LCobeaga/Auto_Rifles/parts/cages and wheels/flywheel smooth 1806.stl

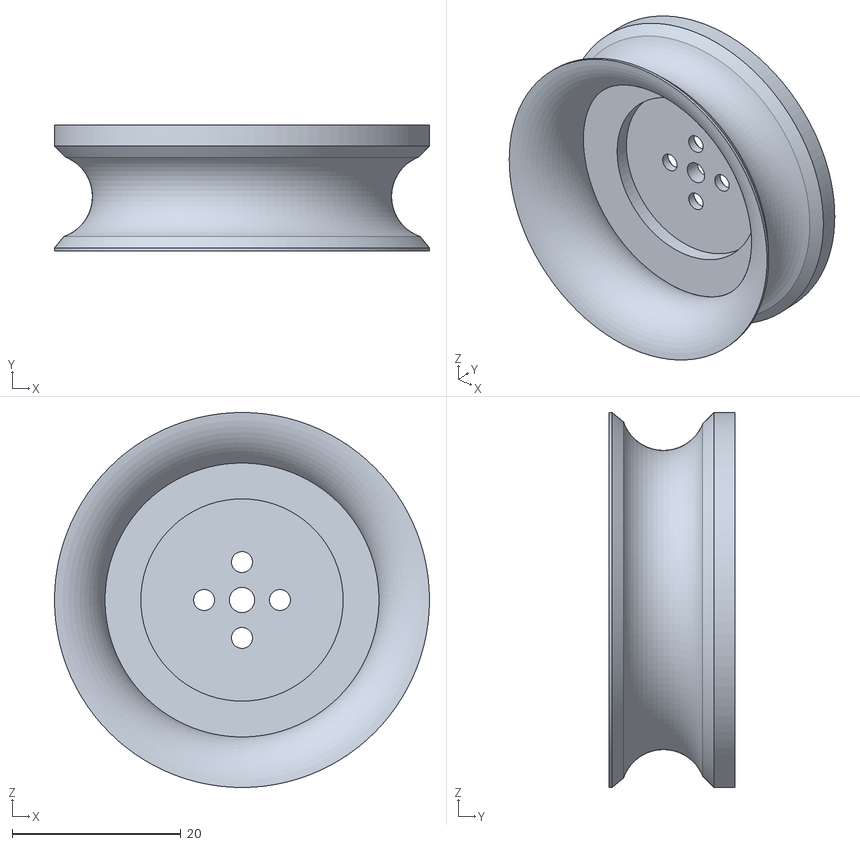
[picture p15: CAD file, 2020-12-02]
parts/cages and wheels/flywheel smooth 1806.stl
44.5 x 15.0 x 44.5
