LCobeaga/Auto_Rifles/parts/front barrel support.stl

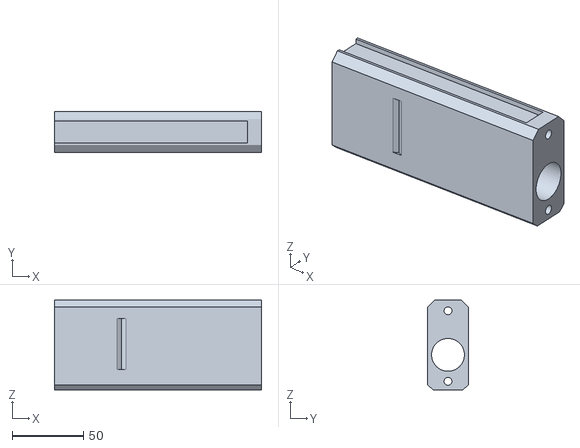
[picture p16: CAD file, 2021-01-24]
parts/front barrel support.stl
145.0 x 28.6 x 63.0
