LCobeaga/Auto_Rifles/parts/Shadow_Price_panels/Stripe right.stl

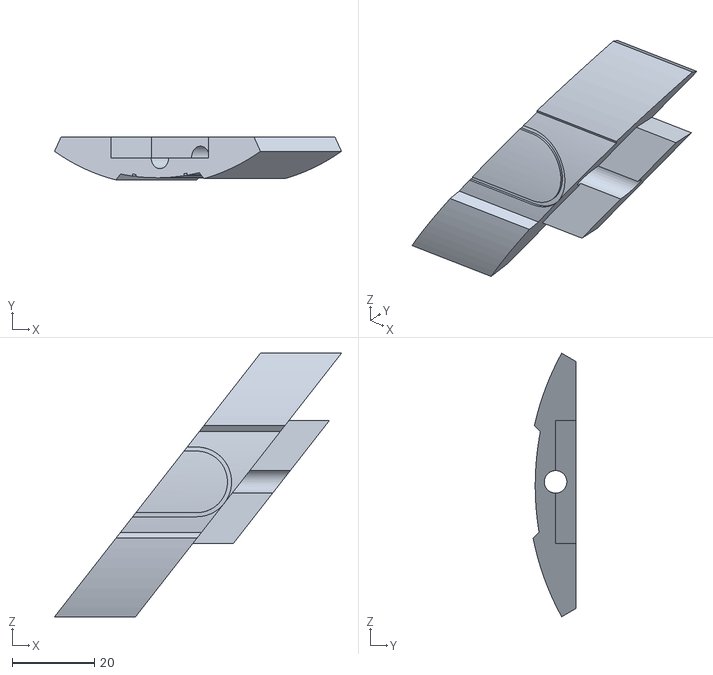
[picture p17: CAD file, 2021-04-09]
parts/Shadow_Price_panels/Stripe right.stl
69.9 x 10.4 x 64.2
