LCobeaga/Auto_Rifles/parts/battery tray.stl

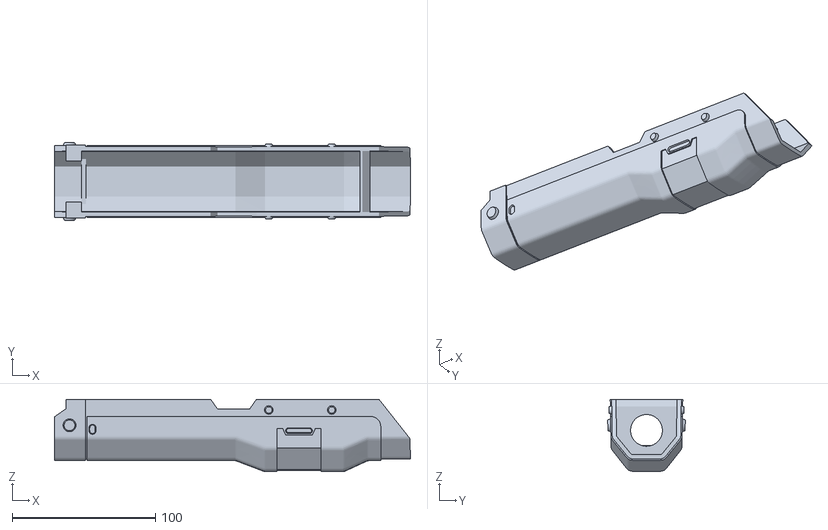
[picture p18: CAD file, 2021-01-12]
parts/battery tray.stl
248.8 x 54.3 x 50.7
