LCobeaga/Auto_Rifles/parts/custom panels/left panel basic.step

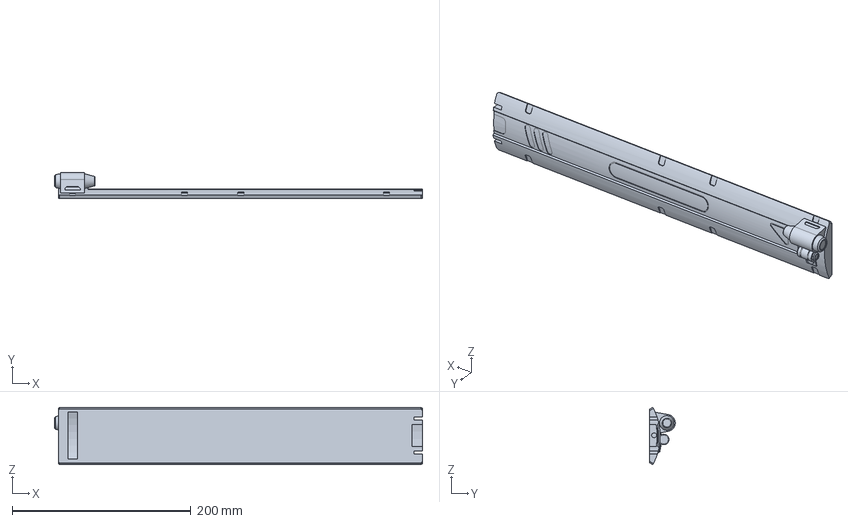
[picture p19: CAD file, 2020-12-09]
parts/custom panels/left panel basic.step
411.5 x 28.7 x 64.2 mm
