LCobeaga/Auto_Rifles/parts/Shadow_Price_panels/Triangle right.stl

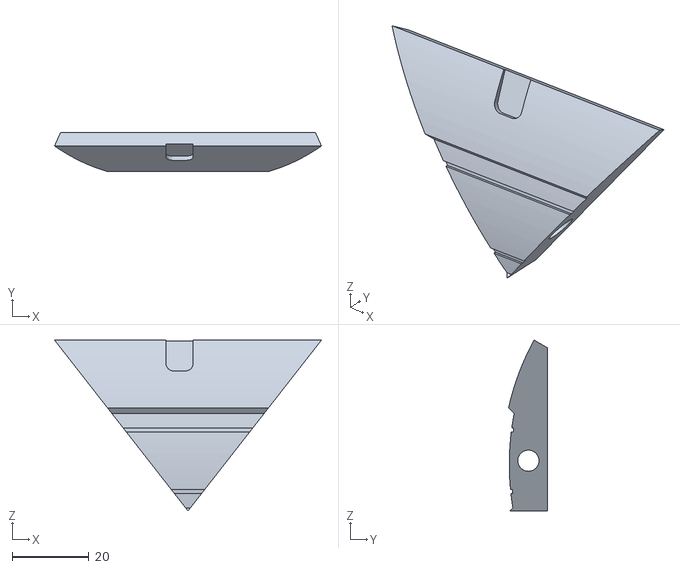
[picture p20: CAD file, 2021-04-09]
parts/Shadow_Price_panels/Triangle right.stl
69.4 x 10.1 x 44.4
