LCobeaga/Auto_Rifles/parts/custom panels/barrel clip modified.step

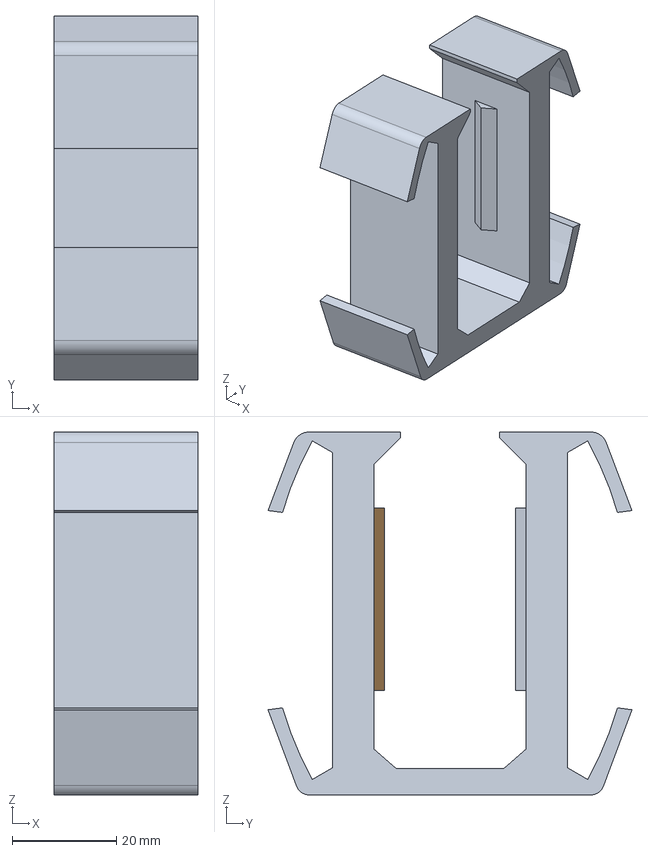
[picture p21: CAD file, 2020-12-09]
parts/custom panels/barrel clip modified.step
27.6 x 69.8 x 69.6 mm
