LCobeaga/Auto_Rifles/parts/lower.stl

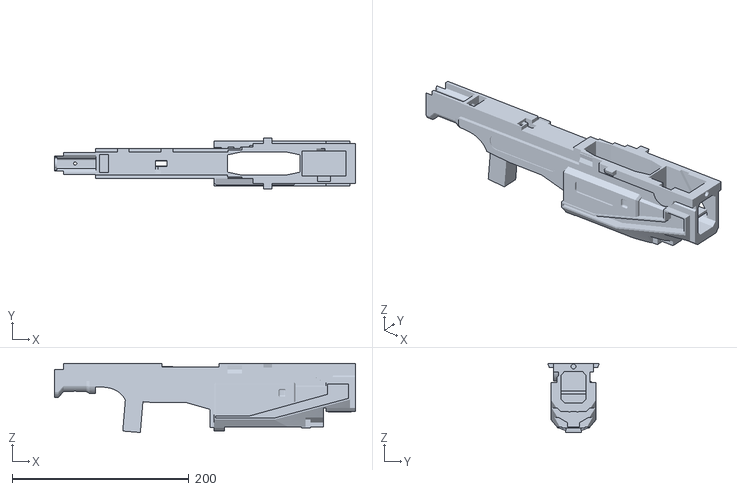
[picture p22: CAD file, 2020-12-02]
parts/lower.stl
340.8 x 58.3 x 78.2
