LCobeaga/Auto_Rifles/parts/Shadow_Price_panels/V left.stl

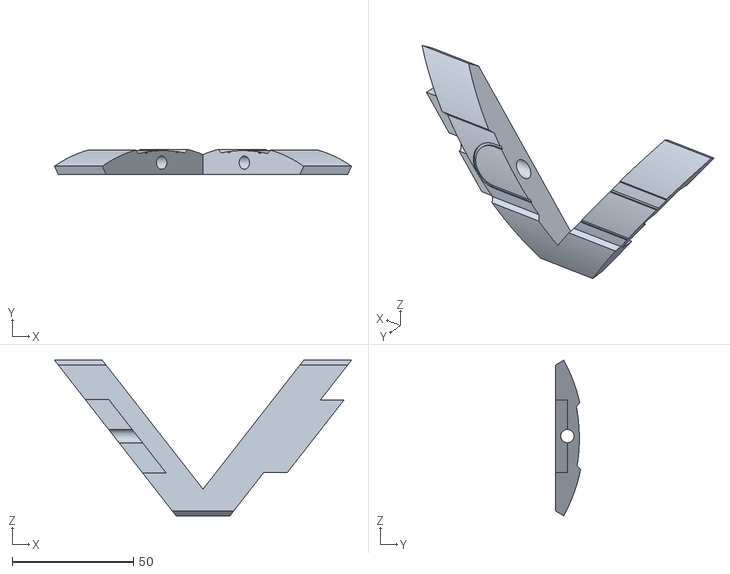
[picture p23: CAD file, 2021-04-09]
parts/Shadow_Price_panels/V left.stl
122.7 x 10.4 x 64.2
