LCobeaga/Auto_Rifles/parts/top cowl.stl

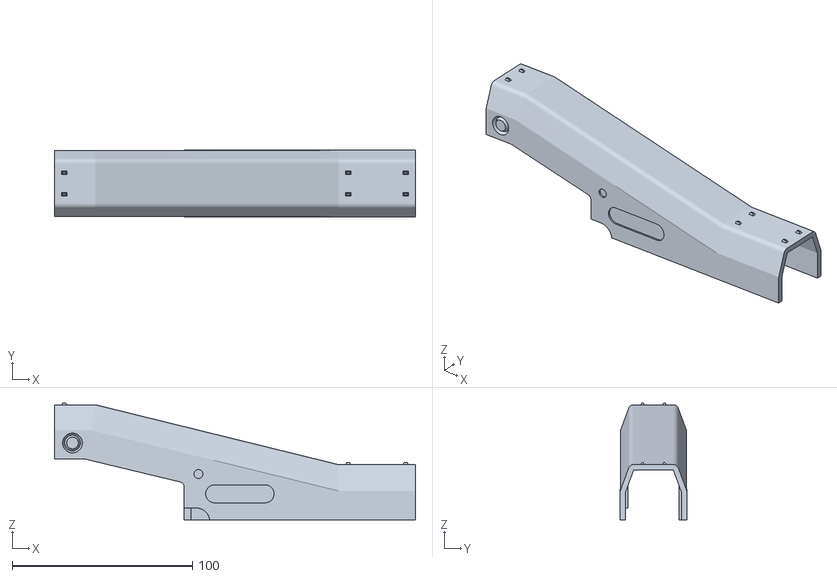
[picture p24: CAD file, 2020-12-02]
parts/top cowl.stl
200.4 x 37.1 x 64.9
