LCobeaga/Auto_Rifles/parts/Shadow_Price_panels/V right.stl

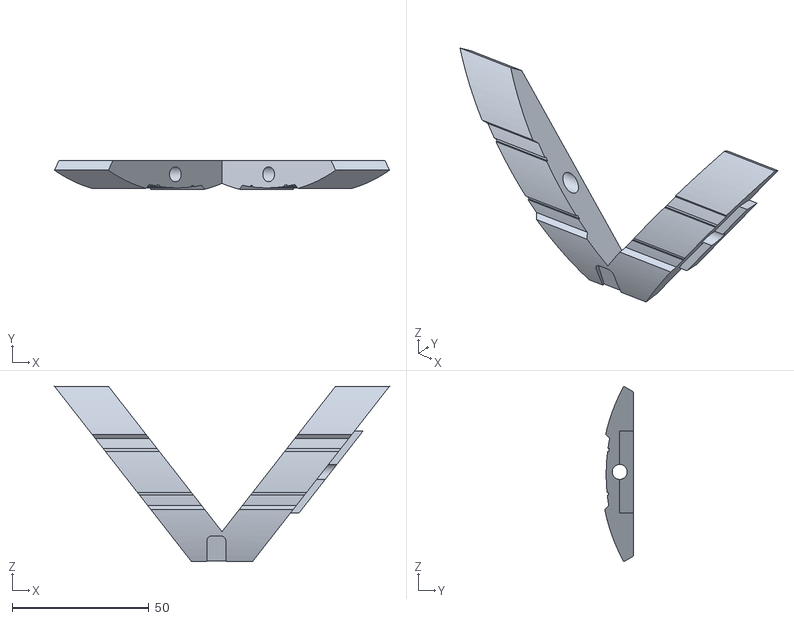
[picture p25: CAD file, 2021-04-09]
parts/Shadow_Price_panels/V right.stl
122.7 x 10.4 x 64.2
