LCobeaga/Auto_Rifles/parts/upper.stl

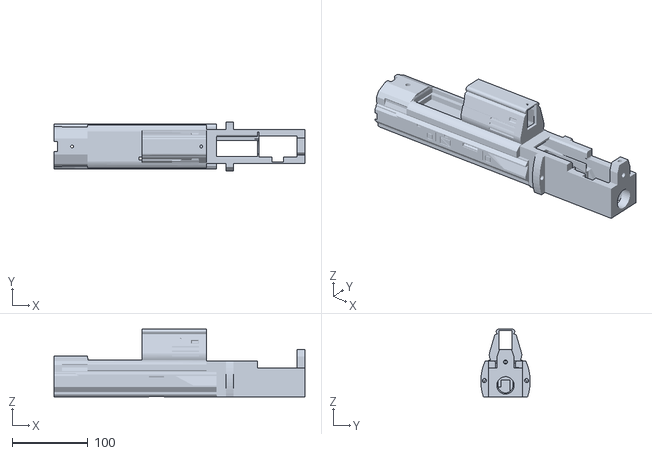
[picture p26: CAD file, 2020-12-02]
parts/upper.stl
331.1 x 65.0 x 89.4
