LCobeaga/Auto_Rifles/parts/archway.stl

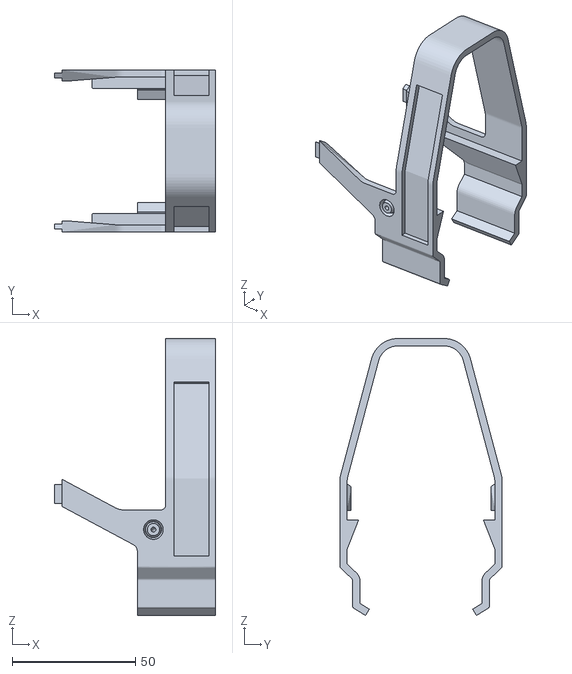
[picture p27: CAD file, 2020-12-02]
parts/archway.stl
65.5 x 66.0 x 112.6
