LCobeaga/Auto_Rifles/parts/Shadow_Price_panels/Back right.stl

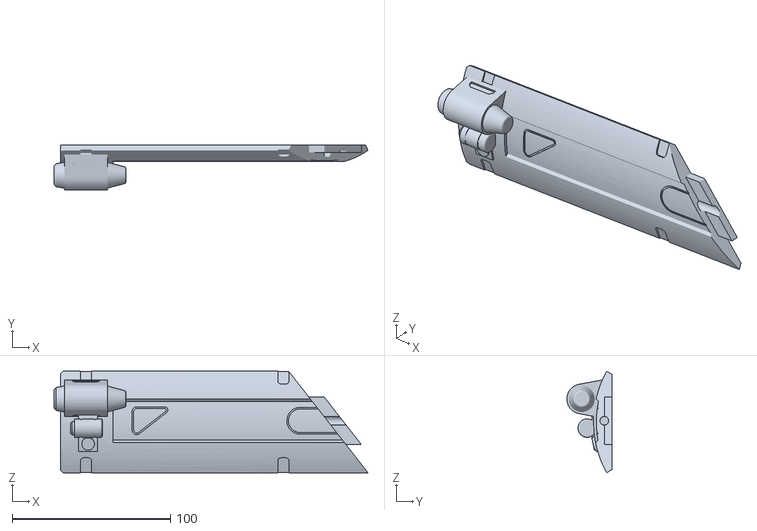
[picture p28: CAD file, 2021-04-09]
parts/Shadow_Price_panels/Back right.stl
198.7 x 28.6 x 64.2
