LCobeaga/Auto_Rifles/parts/Shadow_Price_panels/Stripe Gap right.stl

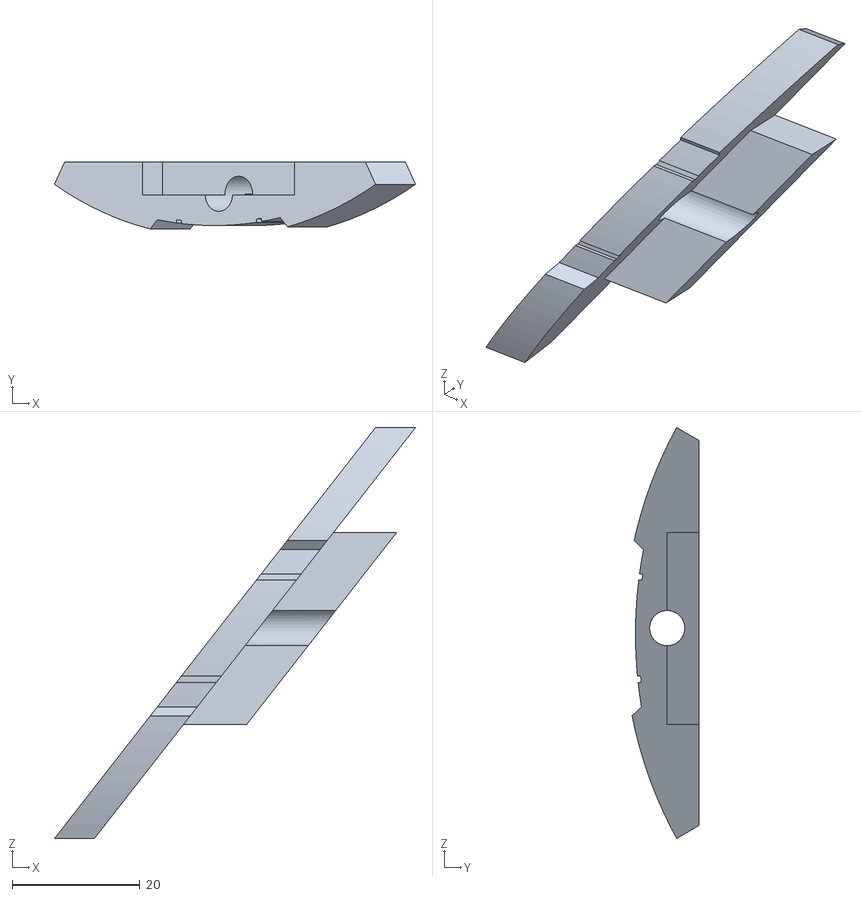
[picture p29: CAD file, 2021-04-09]
parts/Shadow_Price_panels/Stripe Gap right.stl
56.4 x 10.4 x 64.2
