LCobeaga/Auto_Rifles/parts/tail.stl

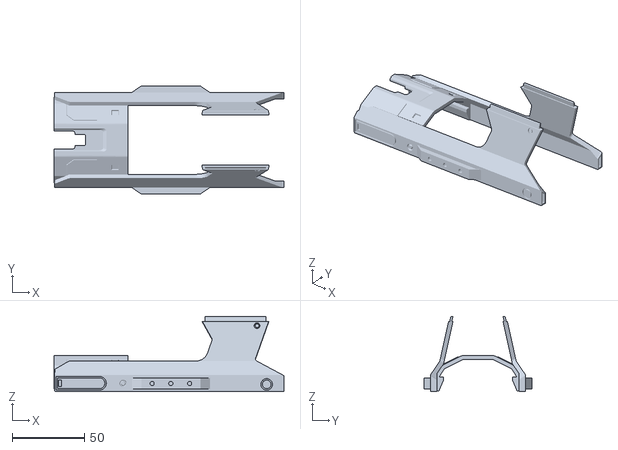
[picture p30: CAD file, 2020-12-02]
parts/tail.stl
159.4 x 75.0 x 52.1
