LCobeaga/Auto_Rifles/parts/2x upper detail.stl

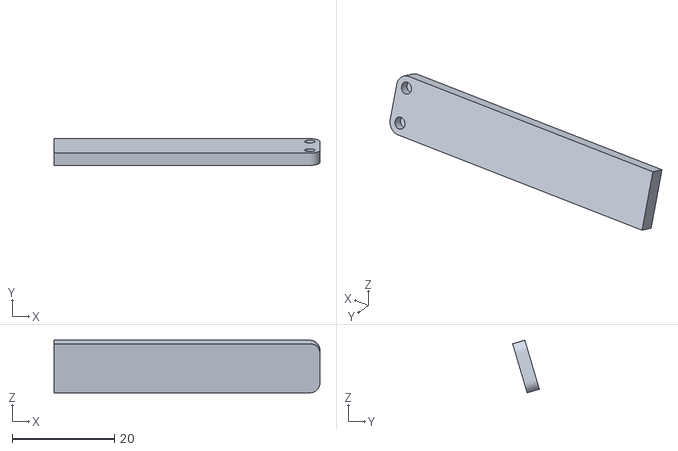
[picture p31: CAD file, 2020-12-02]
parts/2x upper detail.stl
52.0 x 5.24 x 10.3
