LCobeaga/Auto_Rifles/parts/Shadow_Price_panels/Stripe Gap left.stl

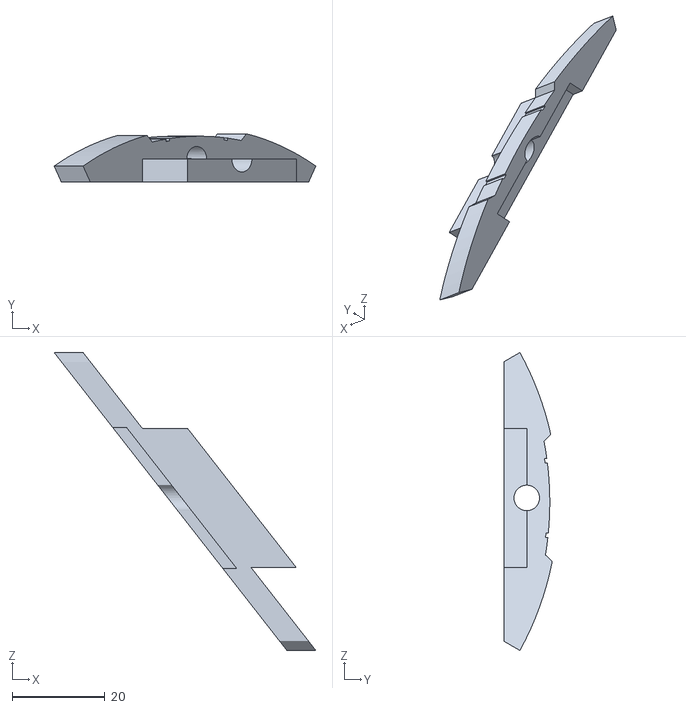
[picture p32: CAD file, 2021-04-09]
parts/Shadow_Price_panels/Stripe Gap left.stl
56.4 x 10.4 x 64.2
