LCobeaga/Auto_Rifles/parts/trigger.stl

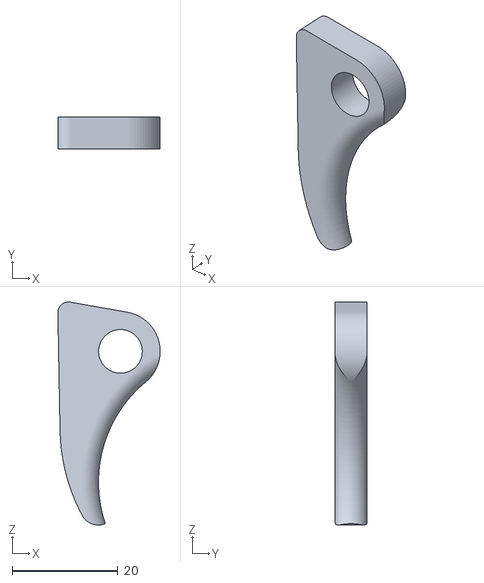
[picture p33: CAD file, 2020-12-02]
parts/trigger.stl
19.3 x 6.00 x 42.1
