LCobeaga/Auto_Rifles/parts/left stock plate.stl

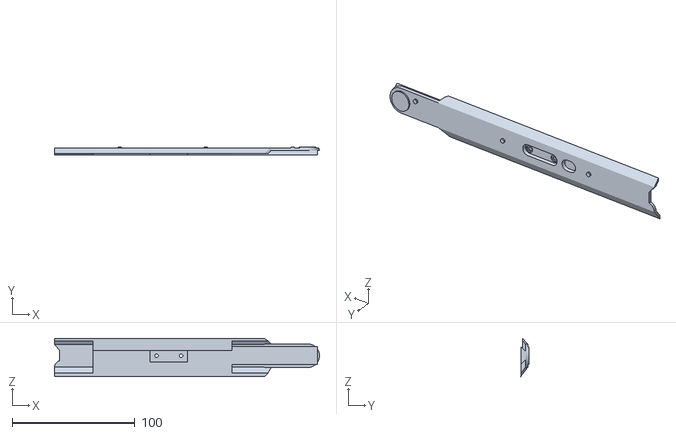
[picture p34: CAD file, 2020-12-02]
parts/left stock plate.stl
216.0 x 6.89 x 31.0
