LCobeaga/Auto_Rifles/parts/mag tooth.stl

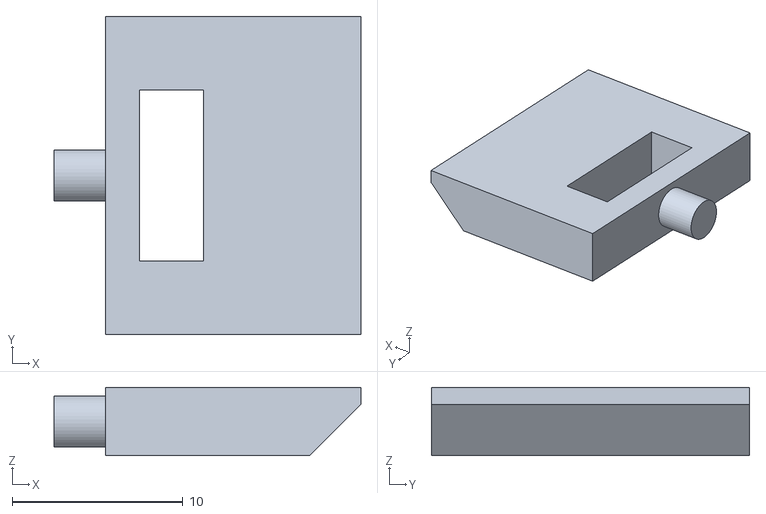
[picture p35: CAD file, 2020-12-02]
parts/mag tooth.stl
17.9 x 18.6 x 4.00
