LCobeaga/Auto_Rifles/parts/middle right loop.stl

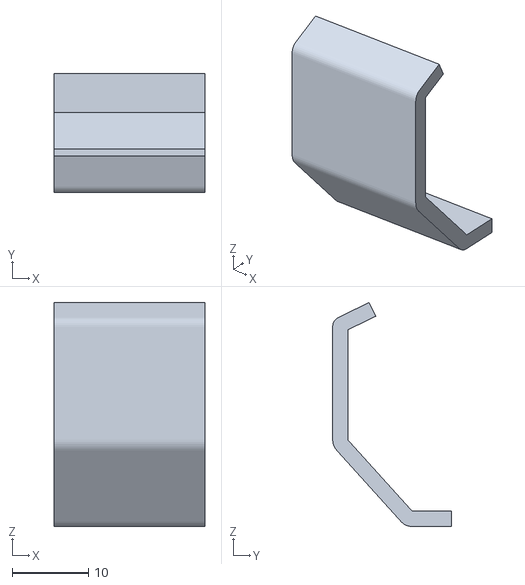
[picture p36: CAD file, 2020-12-02]
parts/middle right loop.stl
19.7 x 15.6 x 29.3
