LCobeaga/Auto_Rifles/parts/knuckle guard bottom.stl

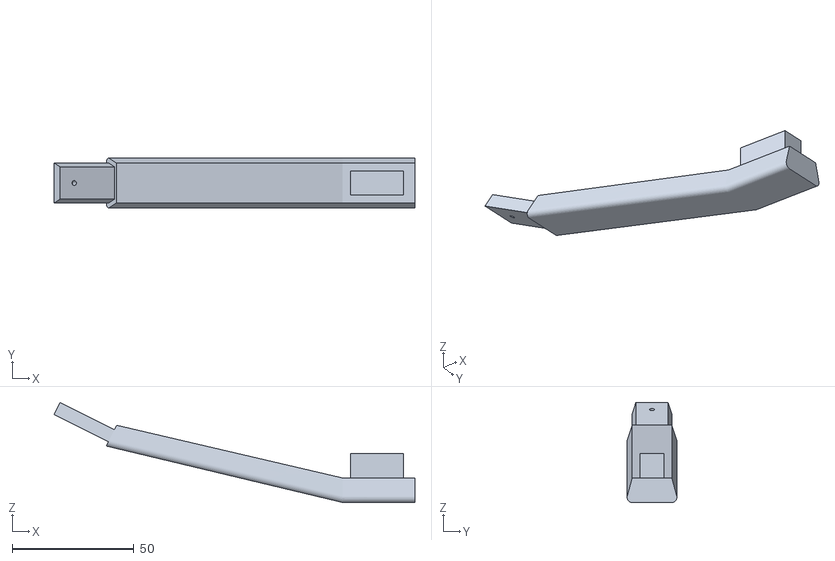
[picture p37: CAD file, 2020-12-02]
parts/knuckle guard bottom.stl
148.5 x 20.5 x 41.1
