LCobeaga/Auto_Rifles/parts/lower filler.stl

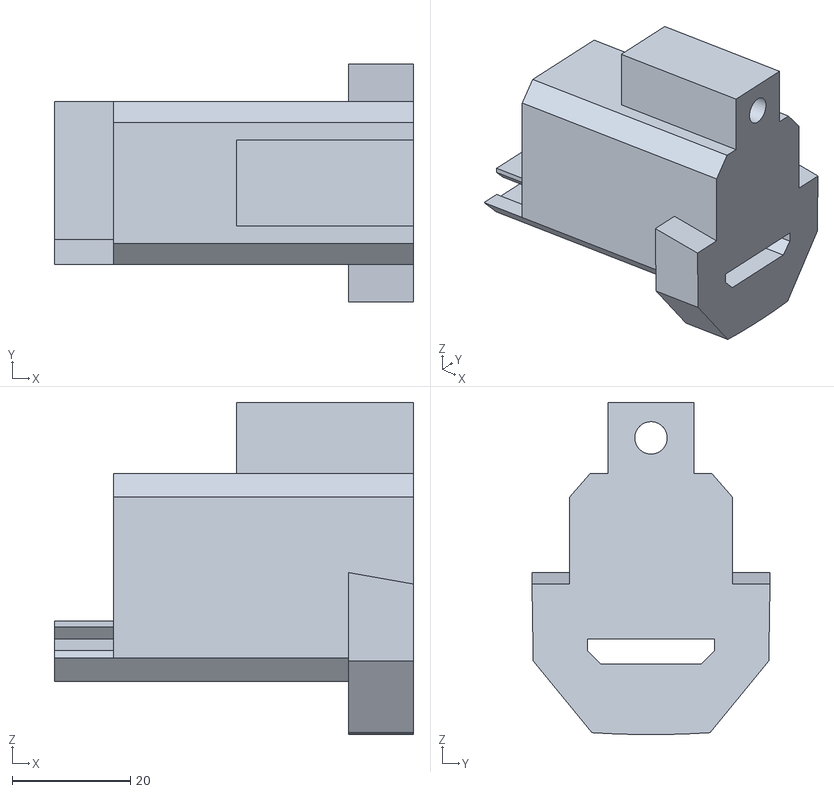
[picture p38: CAD file, 2020-12-02]
parts/lower filler.stl
60.8 x 40.4 x 56.3
