LCobeaga/Auto_Rifles/parts/buttstock.stl

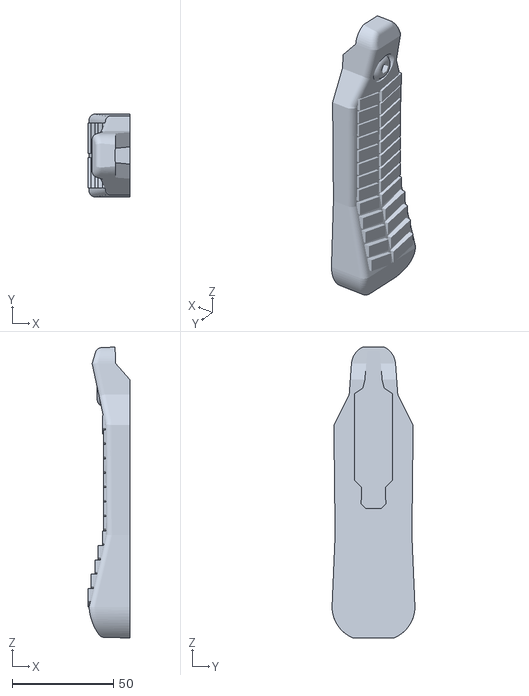
[picture p39: CAD file, 2020-12-02]
parts/buttstock.stl
20.6 x 40.9 x 143.4
