LCobeaga/Auto_Rifles/parts/ammo counter cover.stl

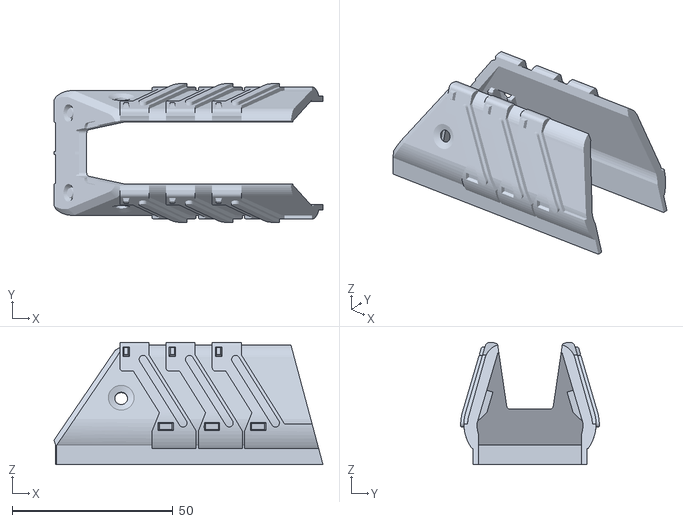
[picture p40: CAD file, 2020-12-02]
parts/ammo counter cover.stl
83.6 x 43.1 x 38.0
