LCobeaga/Auto_Rifles/parts/2x lower detail.stl

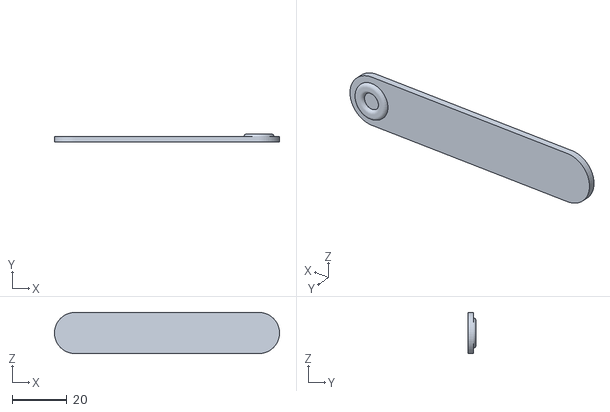
[picture p41: CAD file, 2020-12-02]
parts/2x lower detail.stl
82.0 x 3.00 x 15.0
