LCobeaga/Auto_Rifles/parts/back left greeble.stl

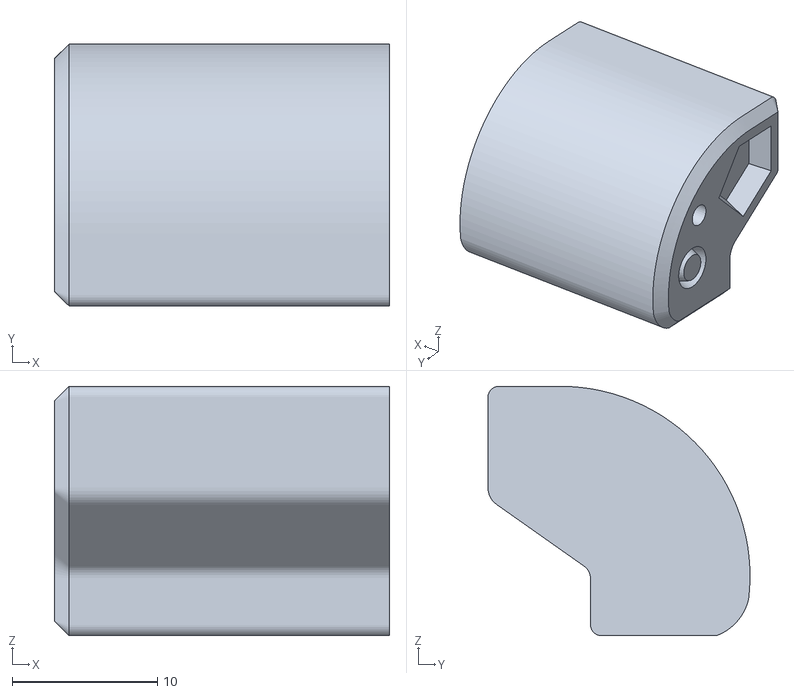
[picture p42: CAD file, 2020-12-02]
parts/back left greeble.stl
23.1 x 18.1 x 17.2
