LCobeaga/Auto_Rifles/parts/barrel low.stl

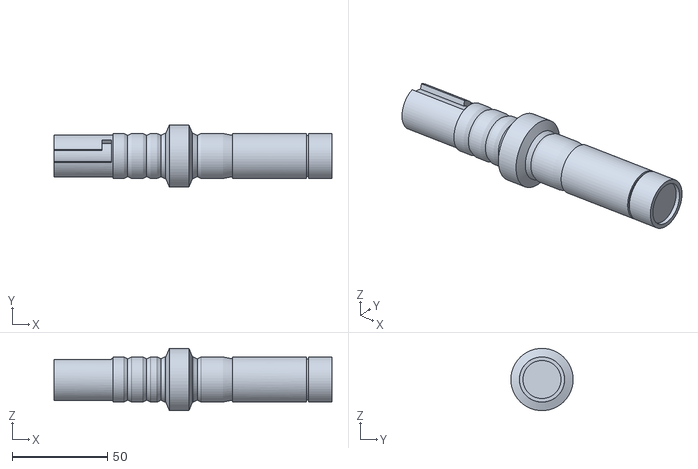
[picture p43: CAD file, 2020-12-02]
parts/barrel low.stl
146.2 x 32.7 x 32.8
