LCobeaga/Auto_Rifles/parts/trigger axle.stl

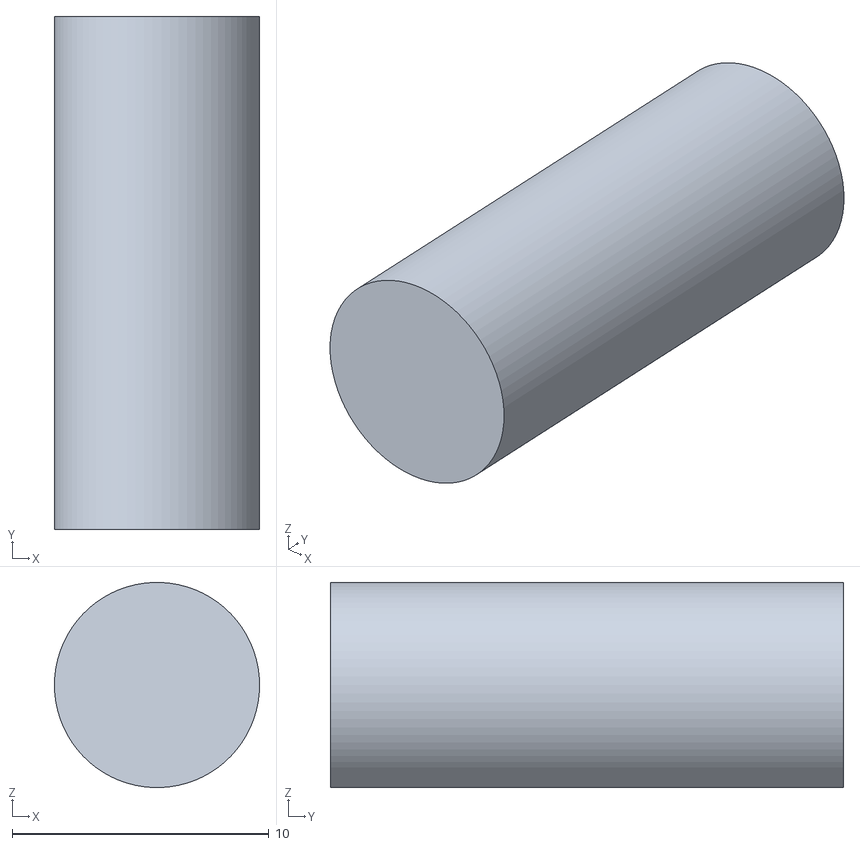
[picture p44: CAD file, 2020-12-02]
parts/trigger axle.stl
8.00 x 20.0 x 7.99
