LCobeaga/Auto_Rifles/parts/right cover detail.stl

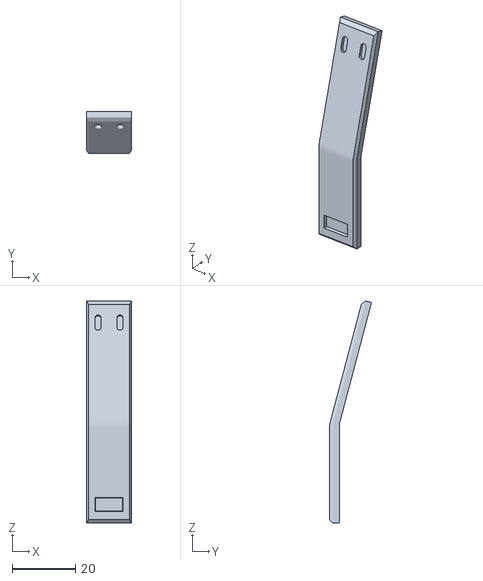
[picture p45: CAD file, 2020-12-02]
parts/right cover detail.stl
14.3 x 13.3 x 70.2
