LCobeaga/Auto_Rifles/parts/stock filler.stl

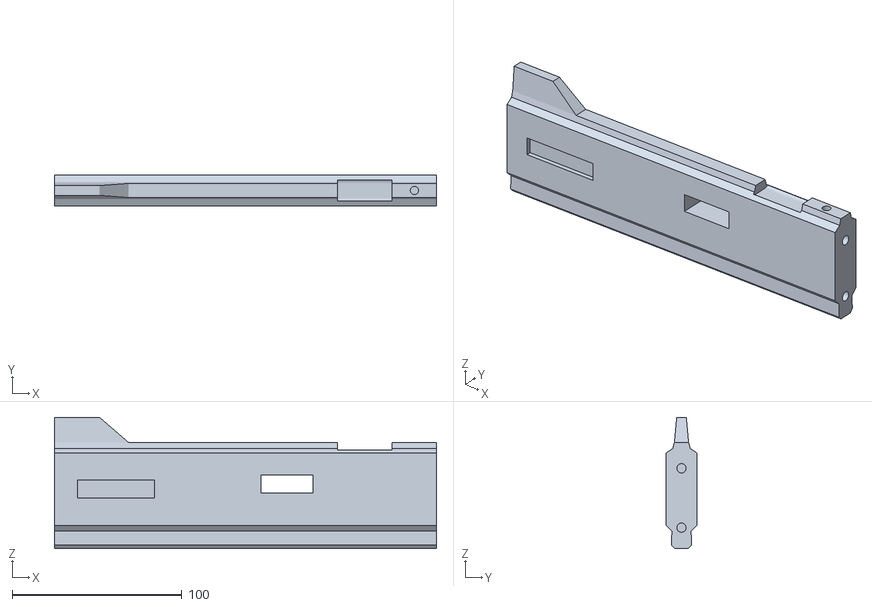
[picture p46: CAD file, 2020-12-02]
parts/stock filler.stl
225.3 x 18.4 x 77.3
