LCobeaga/Auto_Rifles/parts/right panel lock.stl

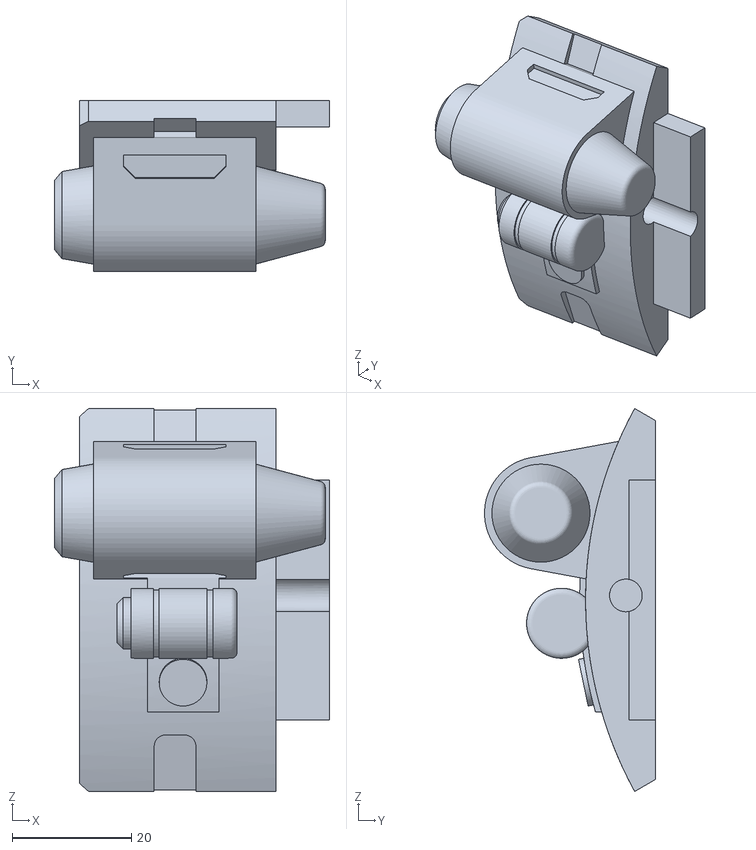
[picture p47: CAD file, 2020-12-02]
parts/right panel lock.stl
46.2 x 28.7 x 64.2
