LCobeaga/Auto_Rifles/parts/left panel back.stl

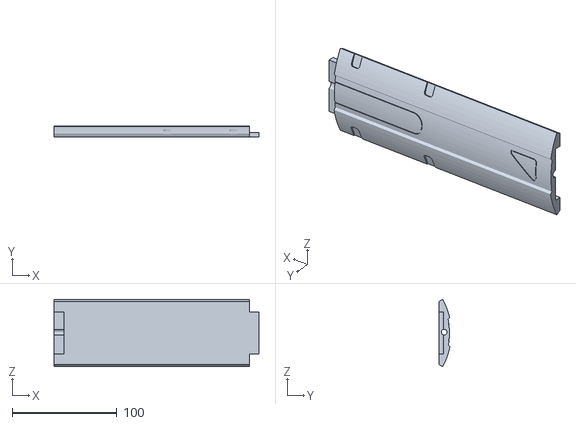
[picture p48: CAD file, 2020-12-02]
parts/left panel back.stl
195.3 x 10.4 x 64.2
