LCobeaga/Auto_Rifles/parts/left panel front.stl

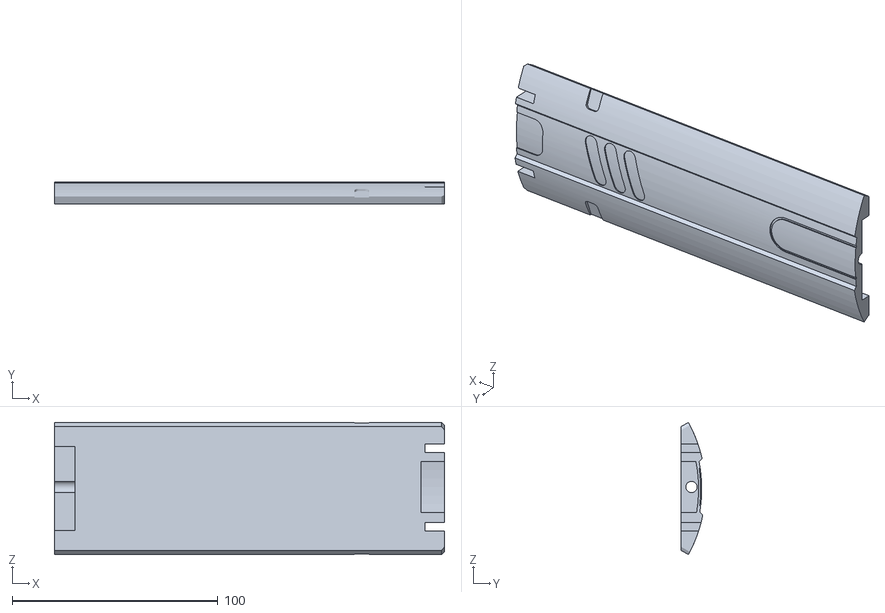
[picture p49: CAD file, 2020-12-02]
parts/left panel front.stl
189.5 x 10.4 x 64.2
