LCobeaga/Auto_Rifles/parts/center filler.stl

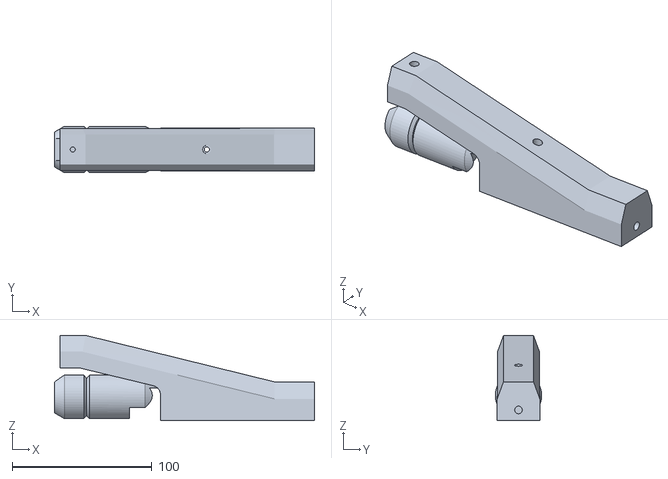
[picture p50: CAD file, 2020-12-02]
parts/center filler.stl
186.0 x 33.1 x 60.9
