LCobeaga/Auto_Rifles/parts/mag release lever.stl

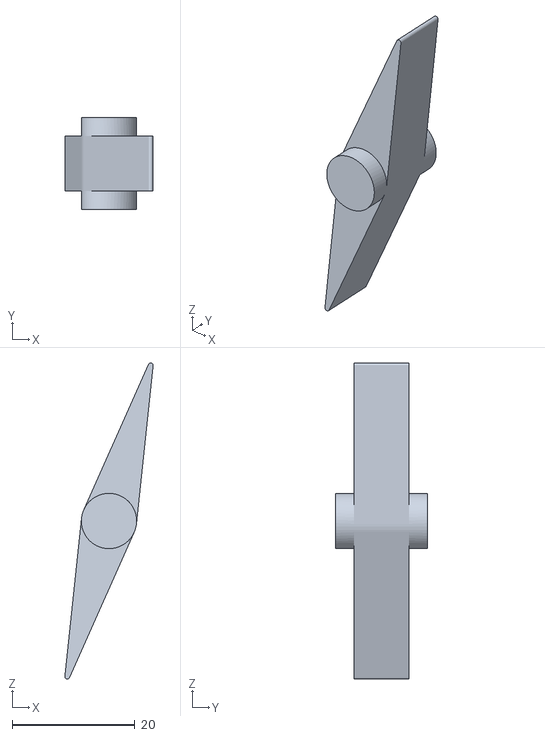
[picture p51: CAD file, 2020-12-02]
parts/mag release lever.stl
14.4 x 15.0 x 51.5
