LCobeaga/Auto_Rifles/parts/back middle greeble.stl

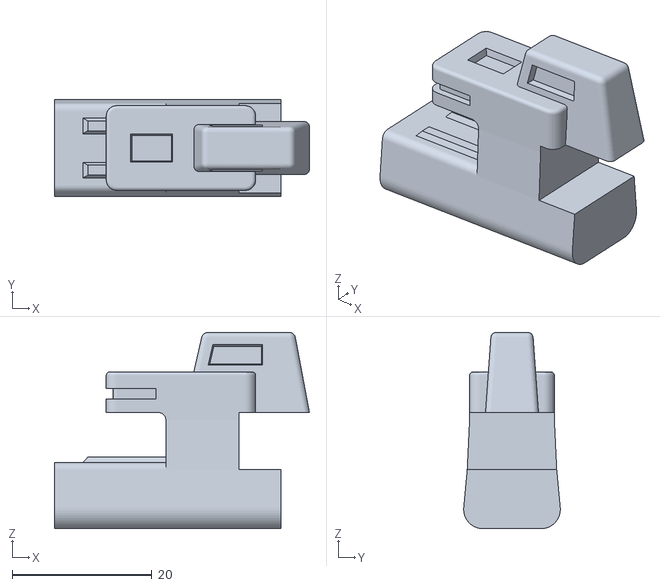
[picture p52: CAD file, 2020-12-02]
parts/back middle greeble.stl
36.5 x 13.8 x 28.1
