LCobeaga/Auto_Rifles/parts/handle left.stl

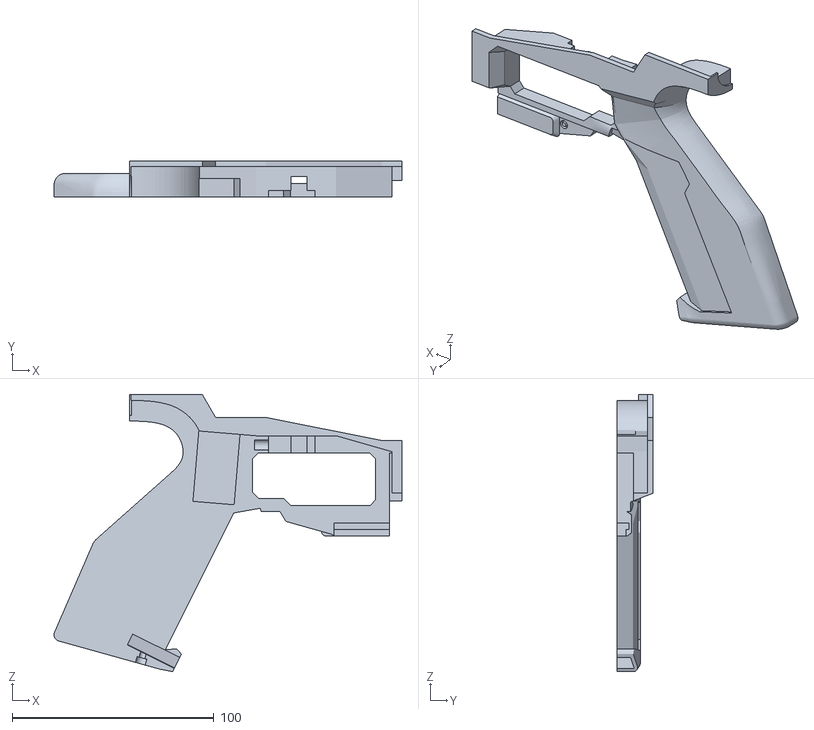
[picture p53: CAD file, 2020-12-02]
parts/handle left.stl
172.6 x 18.0 x 137.5
