LCobeaga/Auto_Rifles/parts/muzzle break.stl

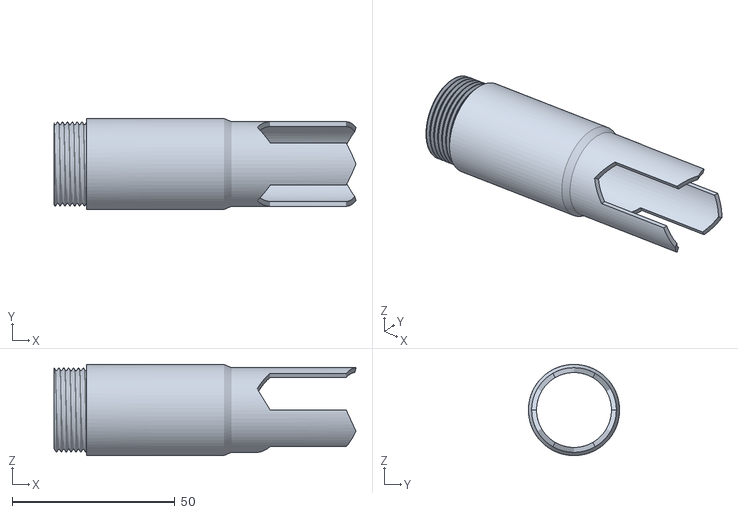
[picture p54: CAD file, 2020-12-02]
parts/muzzle break.stl
92.8 x 28.0 x 28.0
