LCobeaga/Auto_Rifles/parts/left stock strap.stl

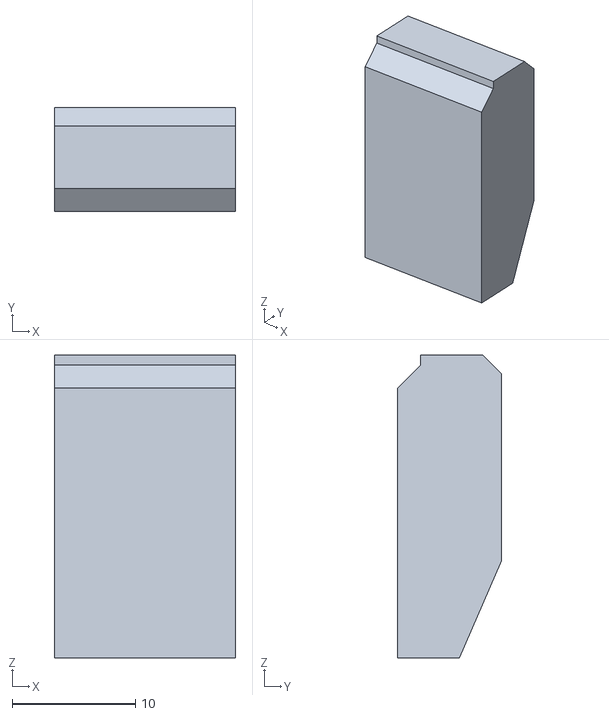
[picture p55: CAD file, 2020-12-02]
parts/left stock strap.stl
14.7 x 8.43 x 24.6
