LCobeaga/Auto_Rifles/parts/stock plate standoff.stl

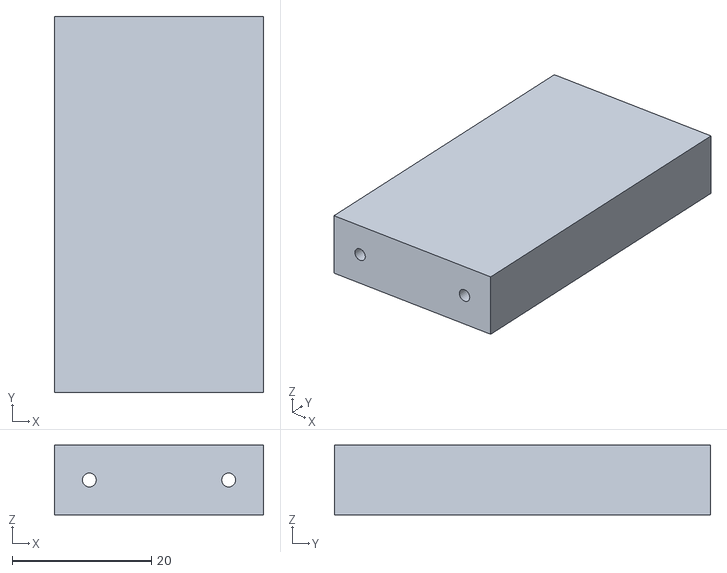
[picture p56: CAD file, 2020-12-02]
parts/stock plate standoff.stl
30.0 x 54.0 x 10.0
