LCobeaga/Auto_Rifles/parts/right gill.stl

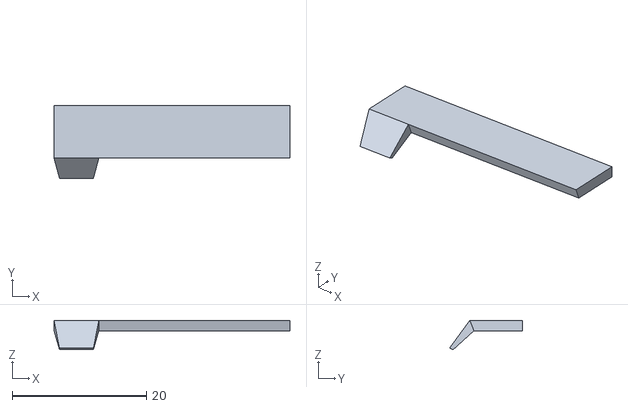
[picture p57: CAD file, 2020-12-02]
parts/right gill.stl
35.1 x 10.8 x 4.37
