LCobeaga/Auto_Rifles/parts/barrel rail.stl

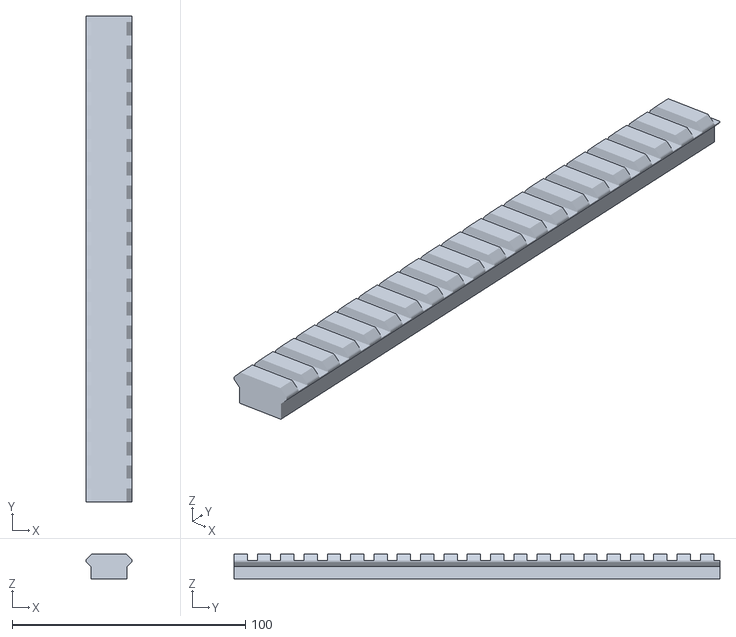
[picture p58: CAD file, 2020-12-02]
parts/barrel rail.stl
19.8 x 208.4 x 10.6
