LCobeaga/Auto_Rifles/parts/handle cover.stl

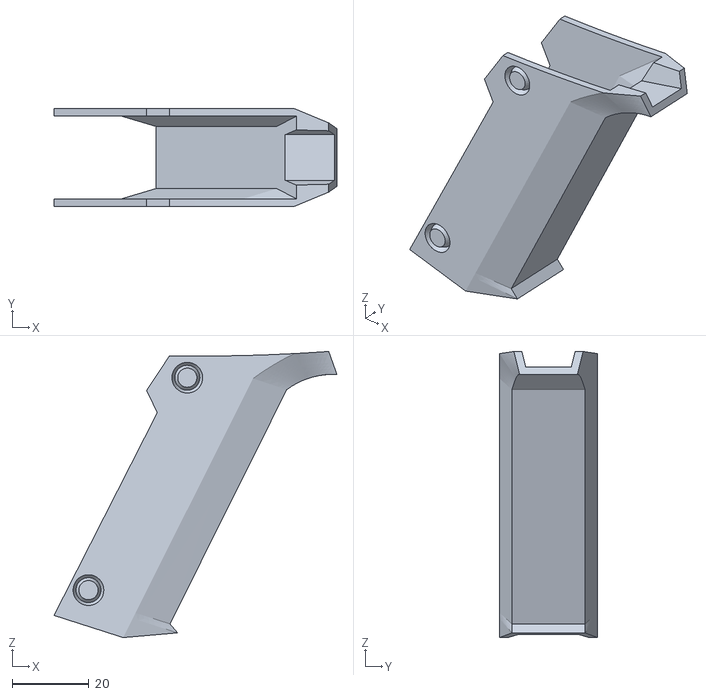
[picture p59: CAD file, 2020-12-02]
parts/handle cover.stl
73.6 x 25.5 x 74.4
