LCobeaga/Auto_Rifles/parts/back locking lug.stl

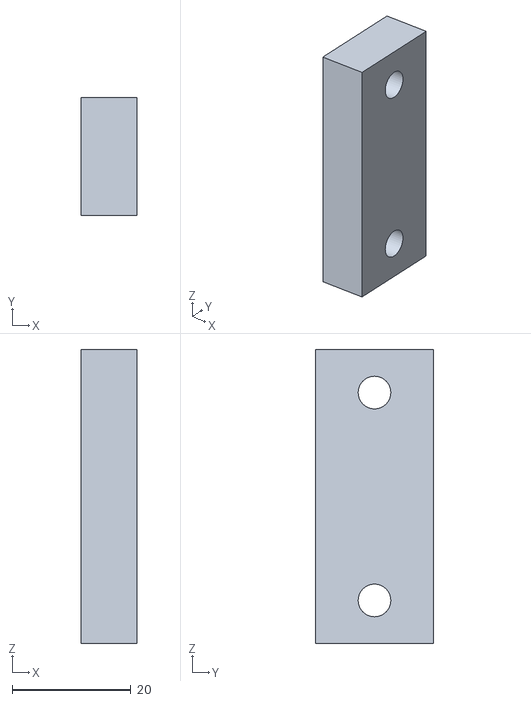
[picture p60: CAD file, 2020-12-02]
parts/back locking lug.stl
9.50 x 19.9 x 49.5
