LCobeaga/Auto_Rifles/parts/battery tray strap.stl

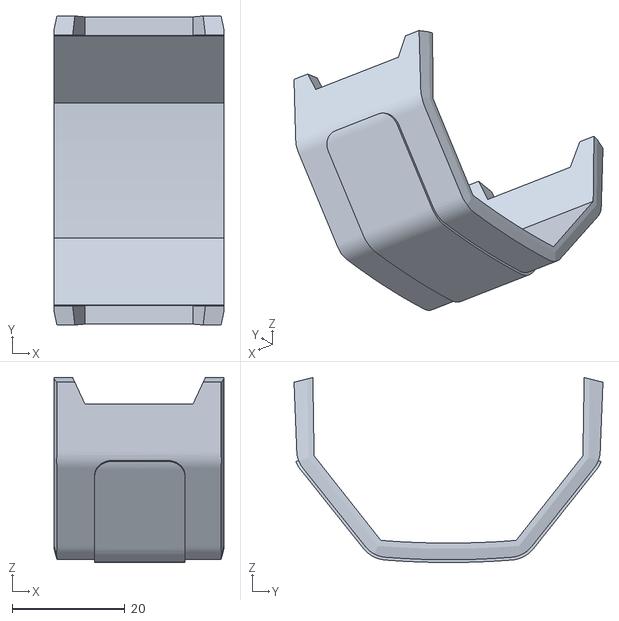
[picture p61: CAD file, 2020-12-02]
parts/battery tray strap.stl
30.1 x 54.7 x 32.8
