LCobeaga/Auto_Rifles/parts/right lower cover.stl

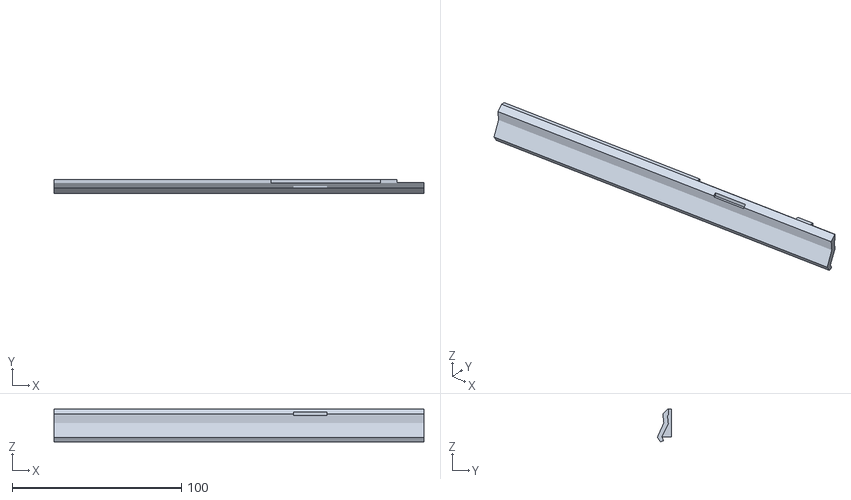
[picture p62: CAD file, 2020-12-02]
parts/right lower cover.stl
218.8 x 8.53 x 19.5
