LCobeaga/Auto_Rifles/parts/handle tab.stl

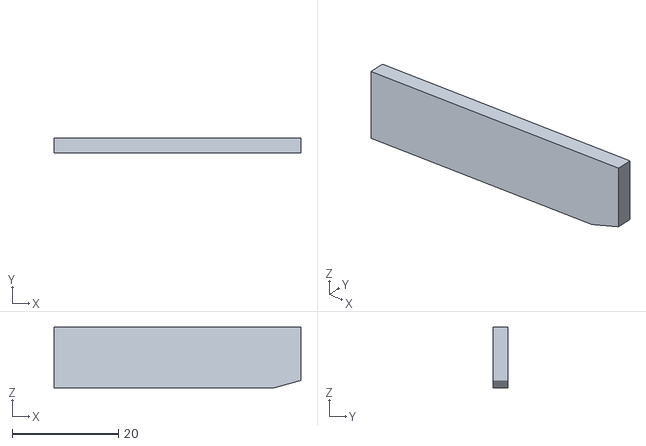
[picture p63: CAD file, 2020-12-02]
parts/handle tab.stl
46.4 x 2.75 x 11.4
