LCobeaga/Auto_Rifles/parts/priming pin.stl

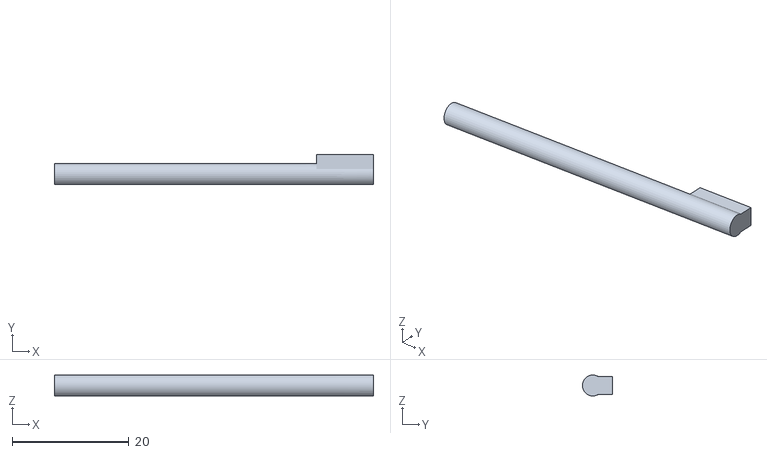
[picture p64: CAD file, 2020-12-02]
parts/priming pin.stl
54.8 x 5.19 x 3.60
