LCobeaga/Auto_Rifles/parts/top picatiny.stl

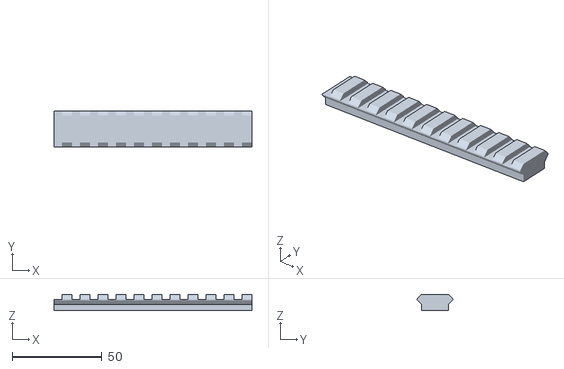
[picture p65: CAD file, 2020-12-02]
parts/top picatiny.stl
110.0 x 19.8 x 9.03
