LCobeaga/Auto_Rifles/parts/stock dovetial.stl

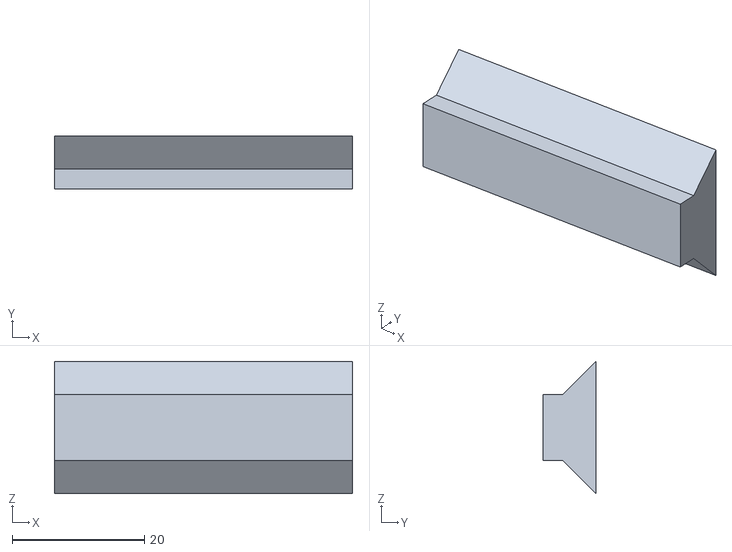
[picture p66: CAD file, 2020-12-02]
parts/stock dovetial.stl
45.0 x 8.00 x 20.0
