LCobeaga/Auto_Rifles/parts/barrel support.stl

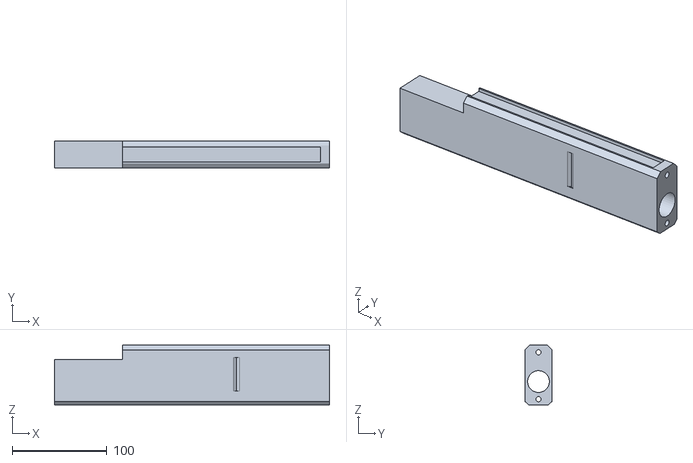
[picture p67: CAD file, 2020-12-02]
parts/barrel support.stl
290.0 x 28.6 x 63.0
