LCobeaga/Auto_Rifles/parts/lock.stl

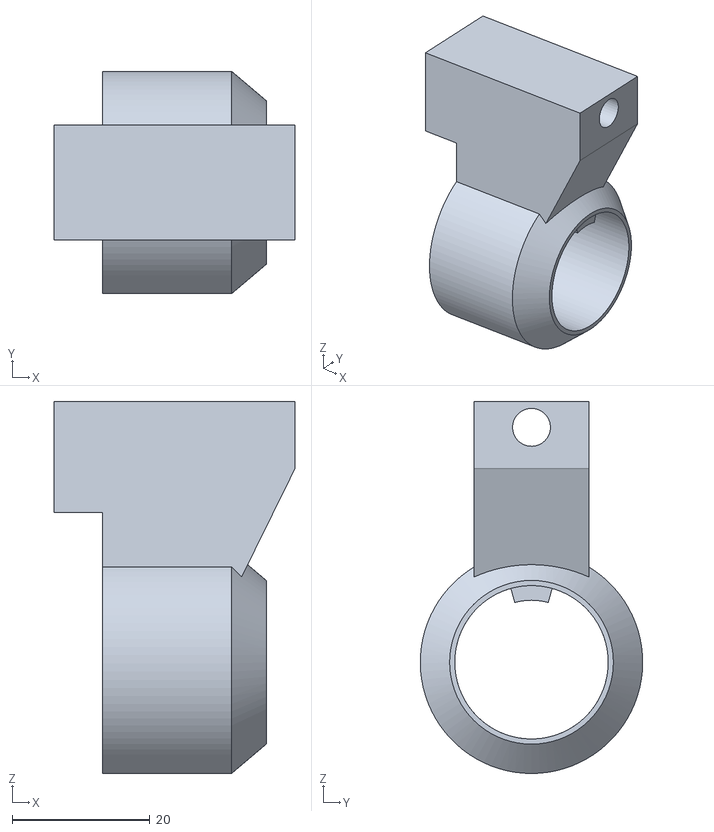
[picture p68: CAD file, 2020-12-02]
parts/lock.stl
34.9 x 32.3 x 54.0
