LCobeaga/Auto_Rifles/parts/detail left magwell.stl

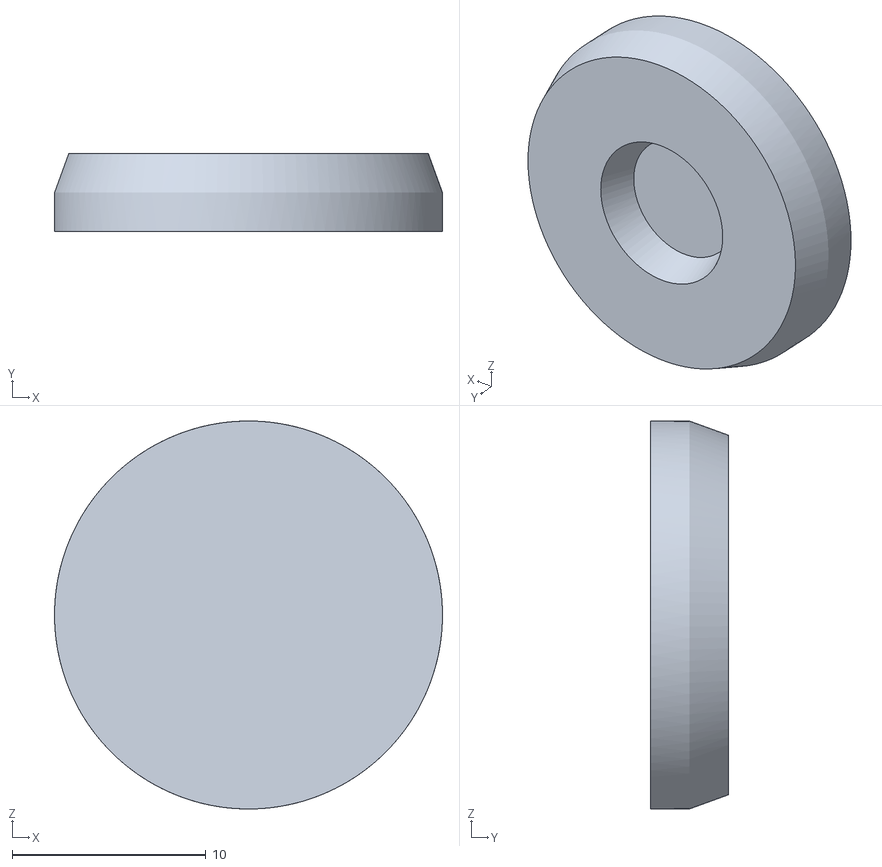
[picture p69: CAD file, 2020-12-02]
parts/detail left magwell.stl
20.0 x 4.00 x 20.0
