LCobeaga/Auto_Rifles/parts/top cover.stl

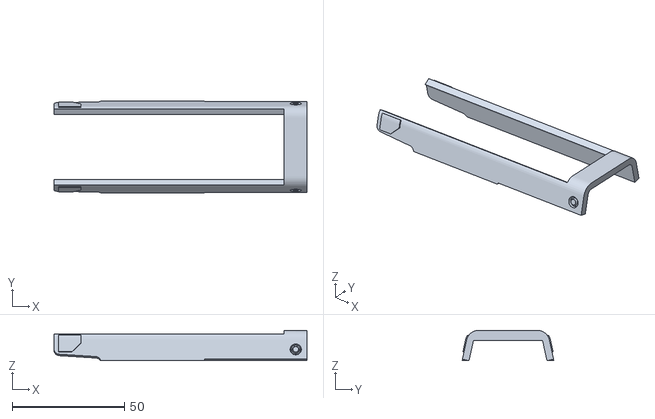
[picture p70: CAD file, 2020-12-02]
parts/top cover.stl
112.5 x 40.8 x 13.5
