LCobeaga/Auto_Rifles/parts/knuckle guard front.stl

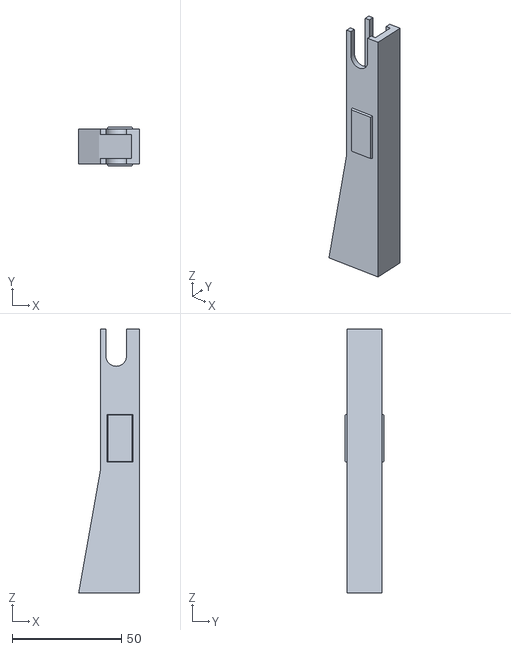
[picture p71: CAD file, 2020-12-02]
parts/knuckle guard front.stl
27.8 x 18.0 x 121.0
