LCobeaga/Auto_Rifles/parts/mag release.stl

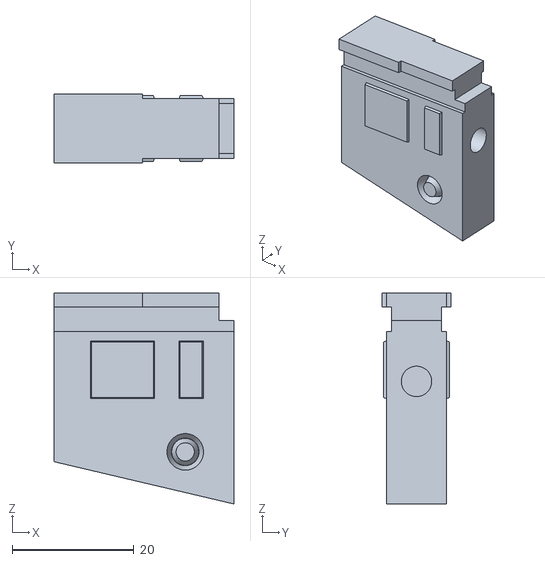
[picture p72: CAD file, 2020-12-02]
parts/mag release.stl
29.5 x 11.3 x 34.6
