LCobeaga/Auto_Rifles/parts/barrel.stl

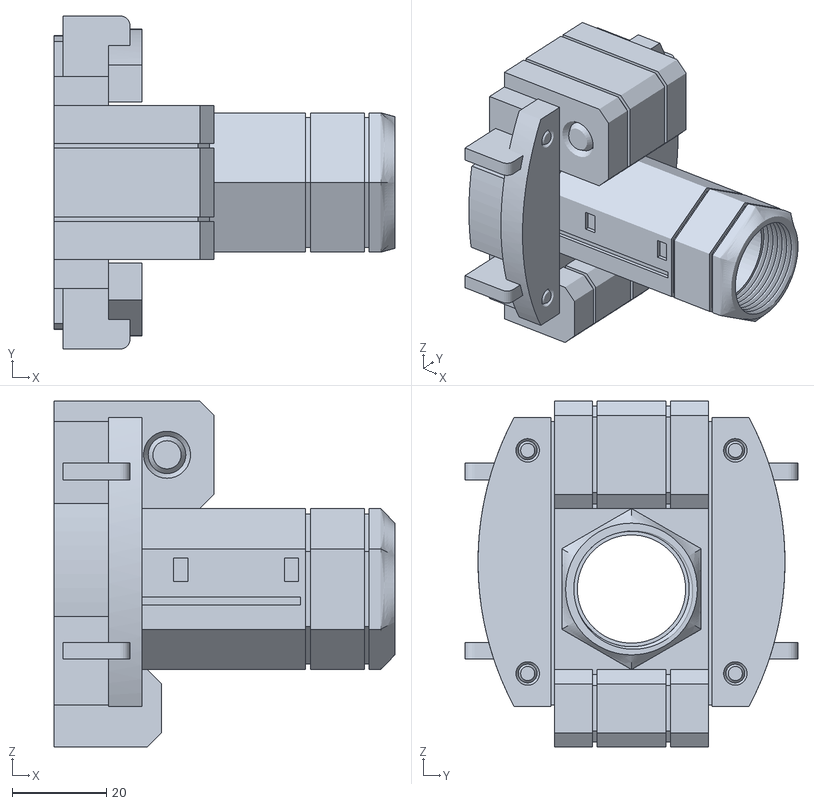
[picture p73: CAD file, 2020-12-02]
parts/barrel.stl
72.5 x 70.8 x 73.5
