LCobeaga/Auto_Rifles/parts/prime.stl

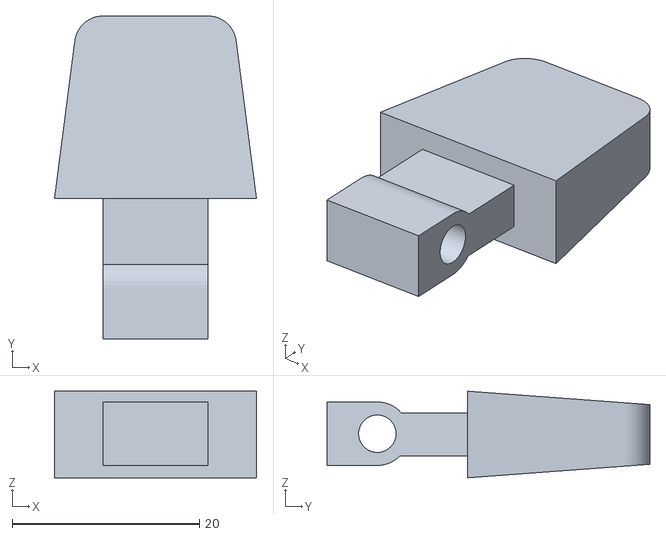
[picture p74: CAD file, 2020-12-02]
parts/prime.stl
21.6 x 34.5 x 9.25
