LCobeaga/Auto_Rifles/parts/locking lug.stl

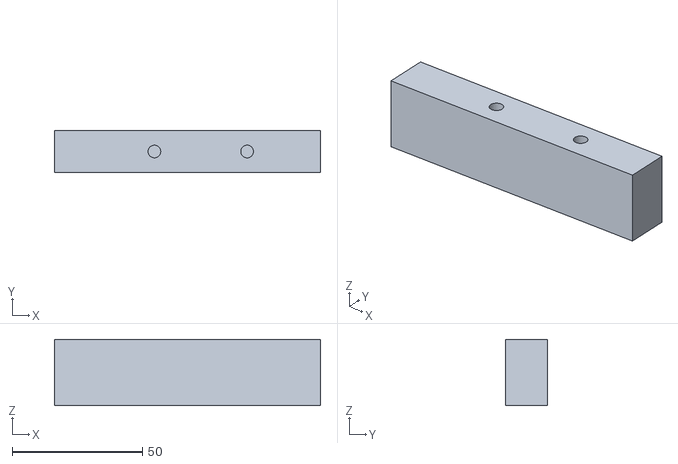
[picture p75: CAD file, 2020-12-02]
parts/locking lug.stl
102.2 x 16.0 x 25.4
