LCobeaga/Auto_Rifles/parts/ammo counter.stl

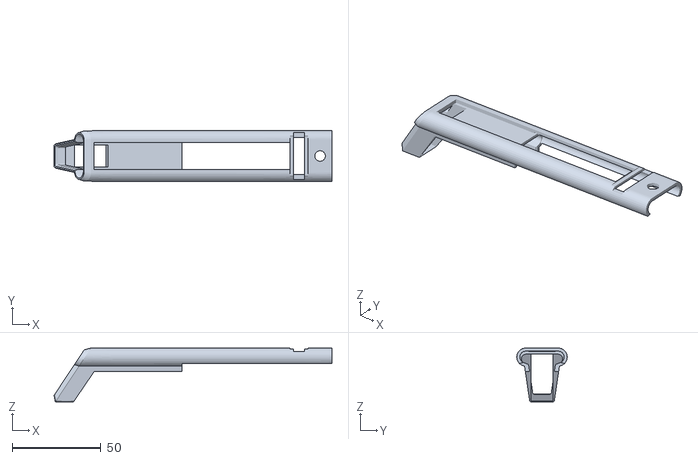
[picture p76: CAD file, 2020-12-02]
parts/ammo counter.stl
157.0 x 28.5 x 30.5
