LCobeaga/Auto_Rifles/parts/barrel clip.stl

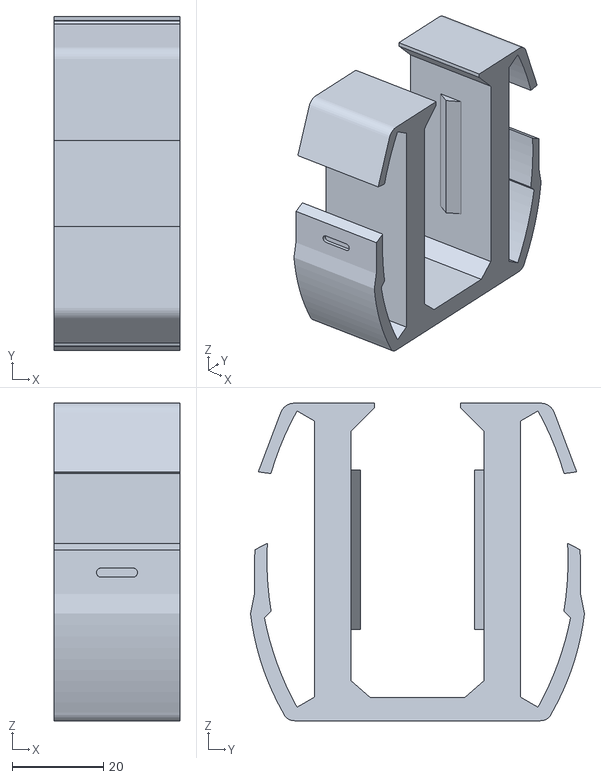
[picture p77: CAD file, 2020-12-02]
parts/barrel clip.stl
27.6 x 73.2 x 69.6
